MouseBiteLabs/Game-Boy-DMG-Color/DMGC-CPU-01/DMGC-CPU-01_2-0_BACK.jpg

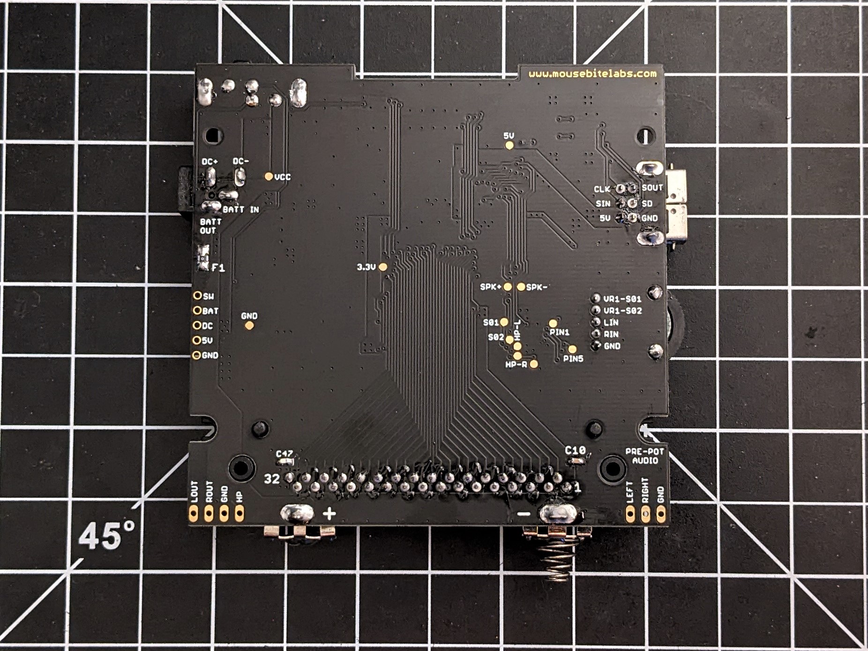
DMGC-CPU-01/DMGC-CPU-01_2-0_BACK.jpg
