MouseBiteLabs/Game-Boy-DMG-Color/DMGC-HDP-01/DMGC-HDP-01_2-0_FRONT.jpg

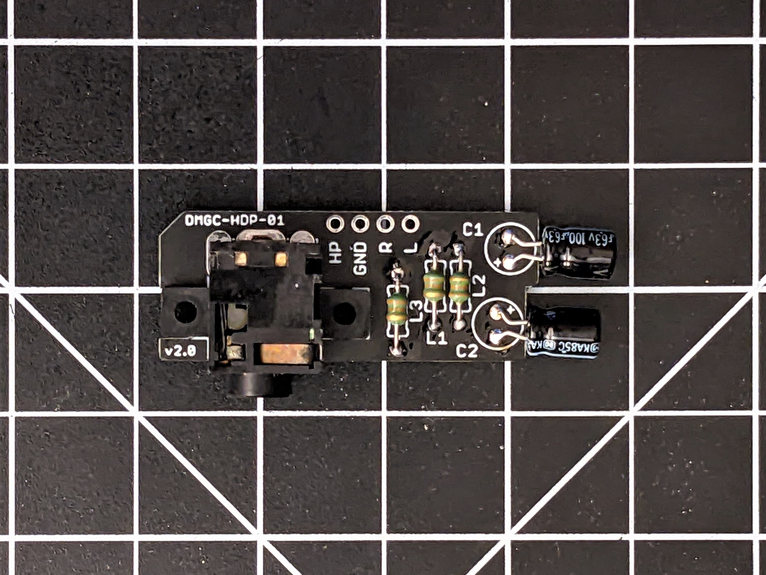
DMGC-HDP-01/DMGC-HDP-01_2-0_FRONT.jpg
