MouseBiteLabs/Game-Boy-DMG-Color/DMGC-IPS-01/DMGC-IPS-01_2-0_FRONT.jpg

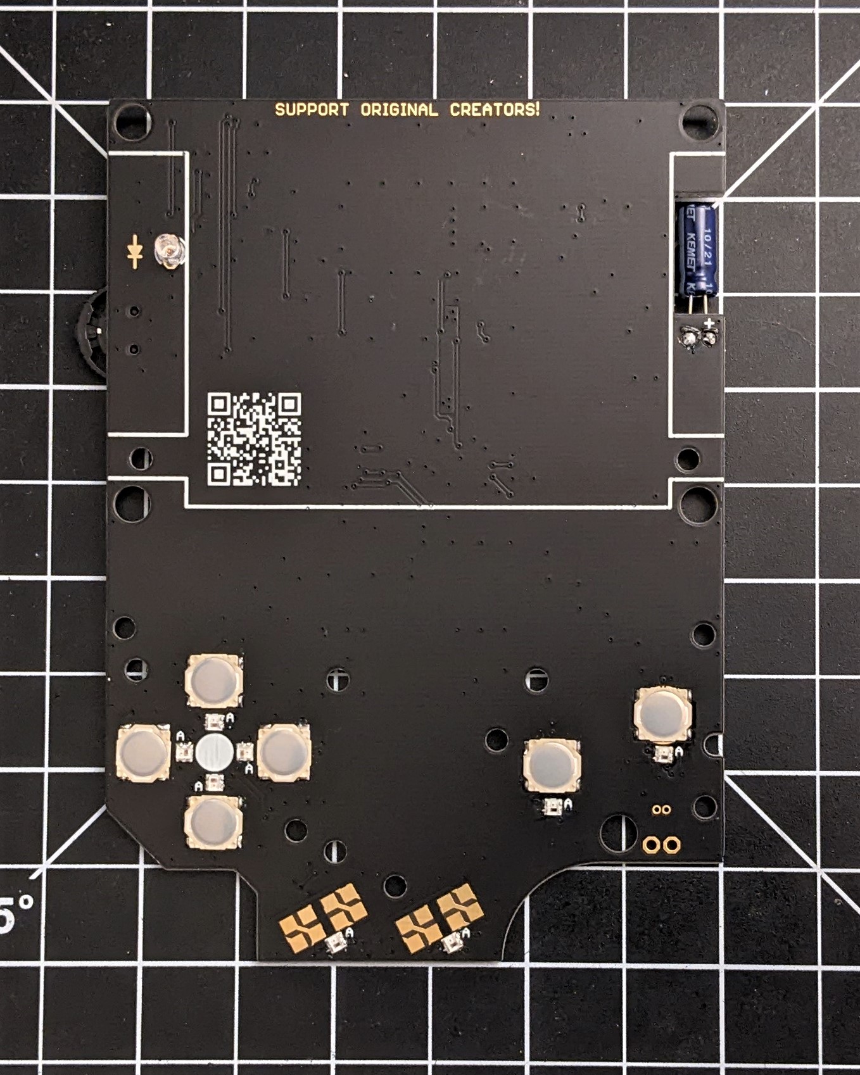
DMGC-IPS-01/DMGC-IPS-01_2-0_FRONT.jpg
